mhorimoto/patrol/KiCAD/M916/M916.kicad_sch

## KiCad design KiCAD/M916/M916.kicad_sch (2023-10-30, an earlier design)

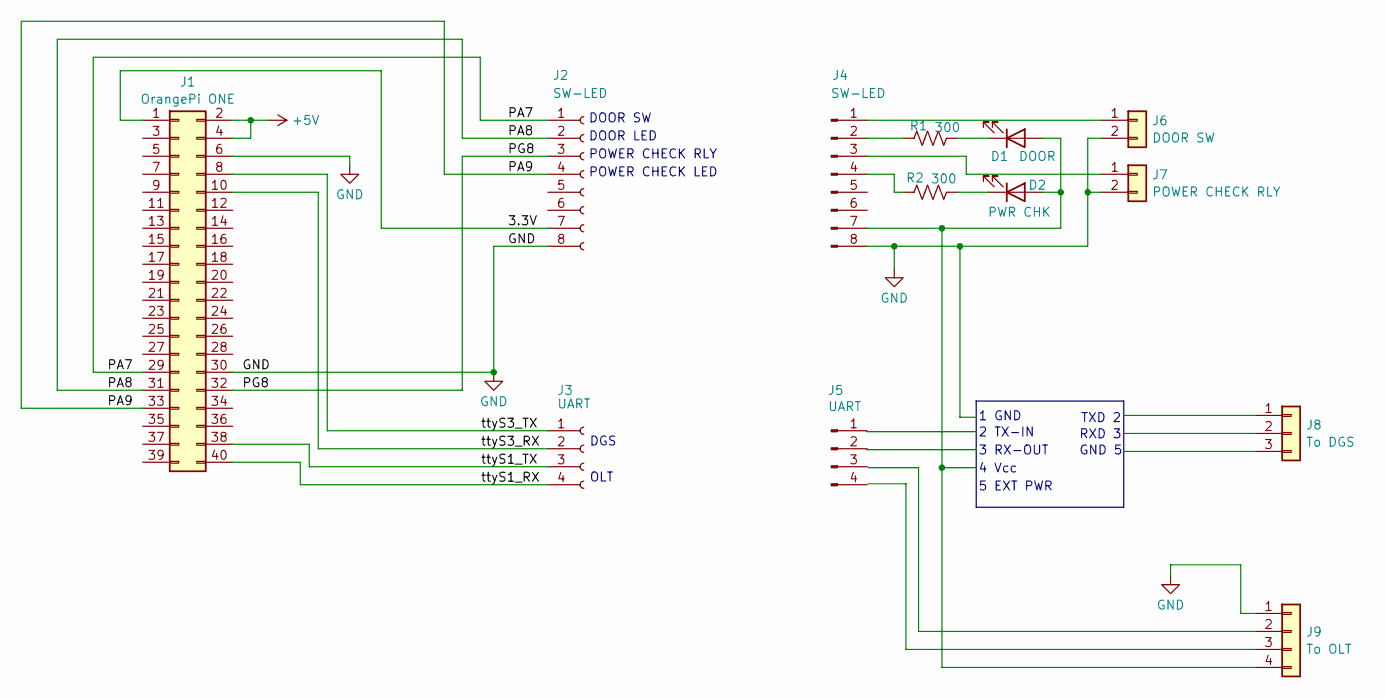
[picture p3: schematic M916.kicad_sch]

Parts:
D1: DOOR
D2: PWR CHK
J1: OrangePi ONE
J2, J4: SW-LED
J3, J5: UART
J6: DOOR SW
J7: POWER CHECK RLY
J8: To DGS
J9: To OLT
R1, R2: 300

Connections:
3.3V: J1.1, J2.7
+5V: J1.2, J1.4
GND: J1.6, J1.30, J2.8, J4.8, J6.2, J7.2, J9.1
unnamed: D1.1 (K), R1.2
unnamed: D1.2 (A), D2.2 (A), J4.7, J9.4
unnamed: D2.1 (K), R2.2
unnamed: J4.1, J6.1
unnamed: J4.2, R1.1
unnamed: J4.3, J7.1
unnamed: J4.4, R2.1
PA7: J1.29, J2.1
PA8: J1.31, J2.2
PA9: J1.33, J2.4
PG8: J1.32, J2.3
ttyS1_RX: J1.40, J3.4
ttyS1_TX: J1.38, J3.3
ttyS3_RX: J1.10, J3.2
ttyS3_TX: J1.8, J3.1

Notes on the sheet:
5 EXT PWR
GND 5
POWER CHECK LED
DOOR LED
OLT
4 Vcc
POWER CHECK RLY
2 TX-IN
3 RX-OUT
1 GND
DGS
DOOR SW
TXD 2
RXD 3
